w7hwh/dxsr8_serial_interface/images/display.png

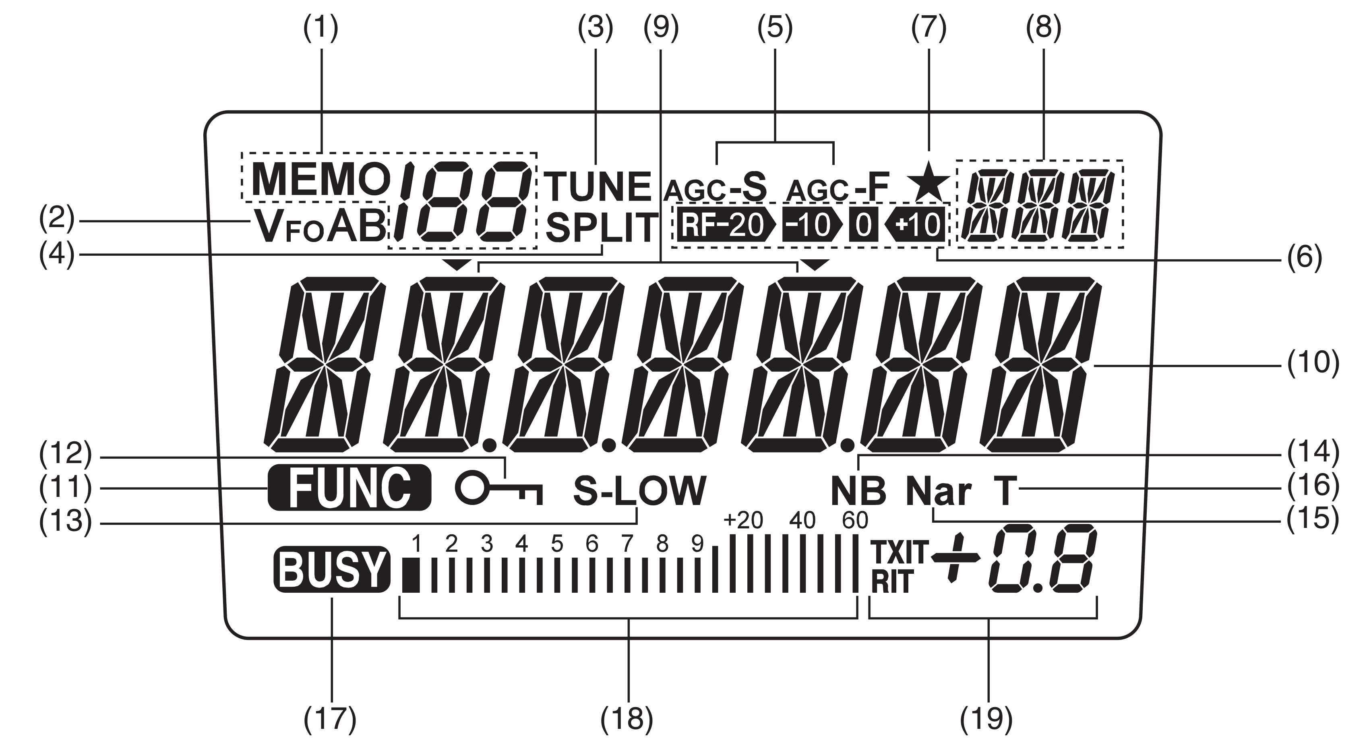
images/display.png
