w7hwh/dxsr8_serial_interface/firmware_c/unique_id.c

/*
 *
 *
 */

#define MMIO16(addr)  (*(volatile uint16_t *)(addr))
#define MMIO32(addr)  (*(volatile uint32_t *)(addr))
#define U_ID          0x1ffff7e8

#include "unique_id.h"

// Read U_ID register 
void unique_id_read(struct u_id *id)
{
    id->off0 = MMIO16(U_ID + 0x0);
    id->off2 = MMIO16(U_ID + 0x2);
    id->off4 = MMIO32(U_ID + 0x4);
    id->off8 = MMIO32(U_ID + 0x8);
}
